devMaxTrauma/Drive/3DModel/ultrasonic-sensors-hc-sr04-1.snapshot.2/133-3.jpg

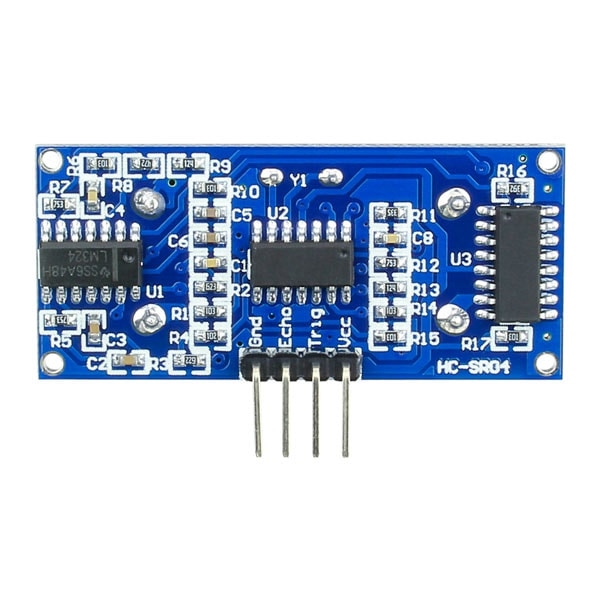
3DModel/ultrasonic-sensors-hc-sr04-1.snapshot.2/133-3.jpg
