devMaxTrauma/Drive/3DModel/ultrasonic-sensors-hc-sr04-1.snapshot.2/back.png

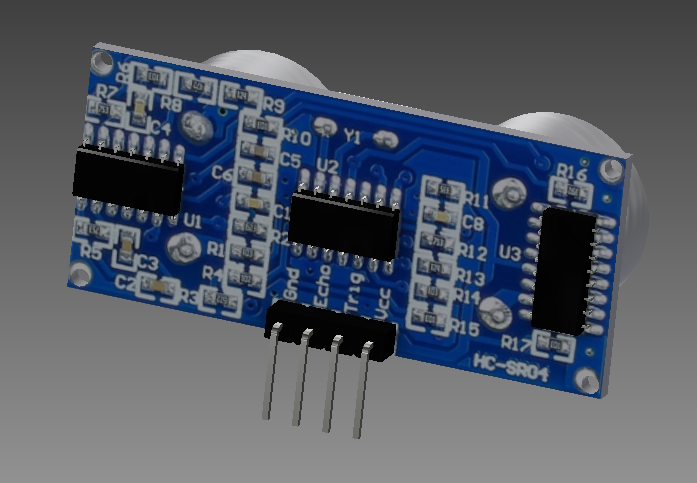
3DModel/ultrasonic-sensors-hc-sr04-1.snapshot.2/back.png
