devMaxTrauma/Drive/3DModel/ultrasonic-sensors-hc-sr04-1.snapshot.2/front.png

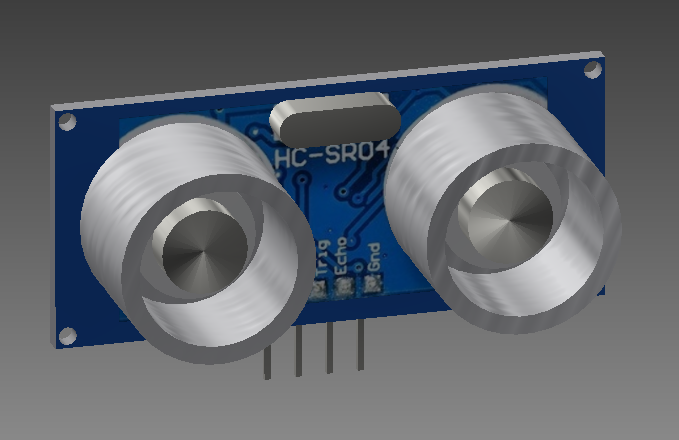
3DModel/ultrasonic-sensors-hc-sr04-1.snapshot.2/front.png
