devMaxTrauma/Drive/3DModel/ultrasonic-sensors-hc-sr04-1.snapshot.2/hc-sr04_.jpg

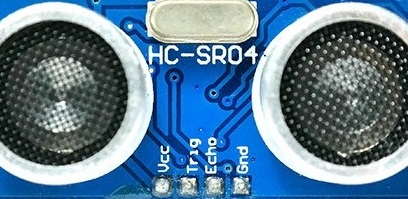
3DModel/ultrasonic-sensors-hc-sr04-1.snapshot.2/hc-sr04_.jpg
