devMaxTrauma/Drive/3DModel/usb-c-female-jrc-b008-1.snapshot.5/USB-C board JRC-B008.png

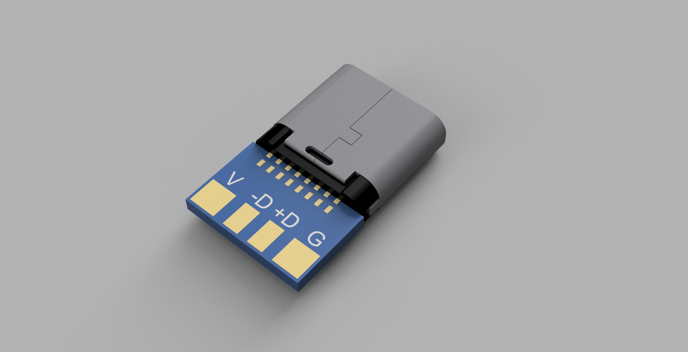
3DModel/usb-c-female-jrc-b008-1.snapshot.5/USB-C board JRC-B008.png
