devMaxTrauma/Drive/BlackBoard/vision layout.png

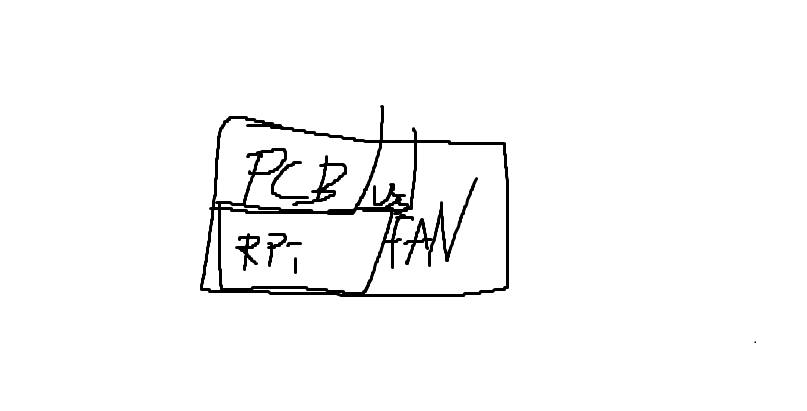
BlackBoard/vision layout.png
