devMaxTrauma/Drive/BlackBoard/상상도.png

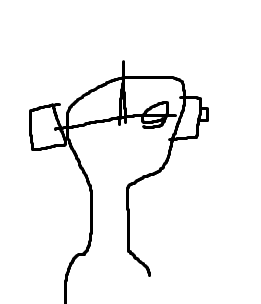
BlackBoard/상상도.png
