devMaxTrauma/Drive/Documents/rOS code new/ROS 24_09_30 code_page-0060.jpg

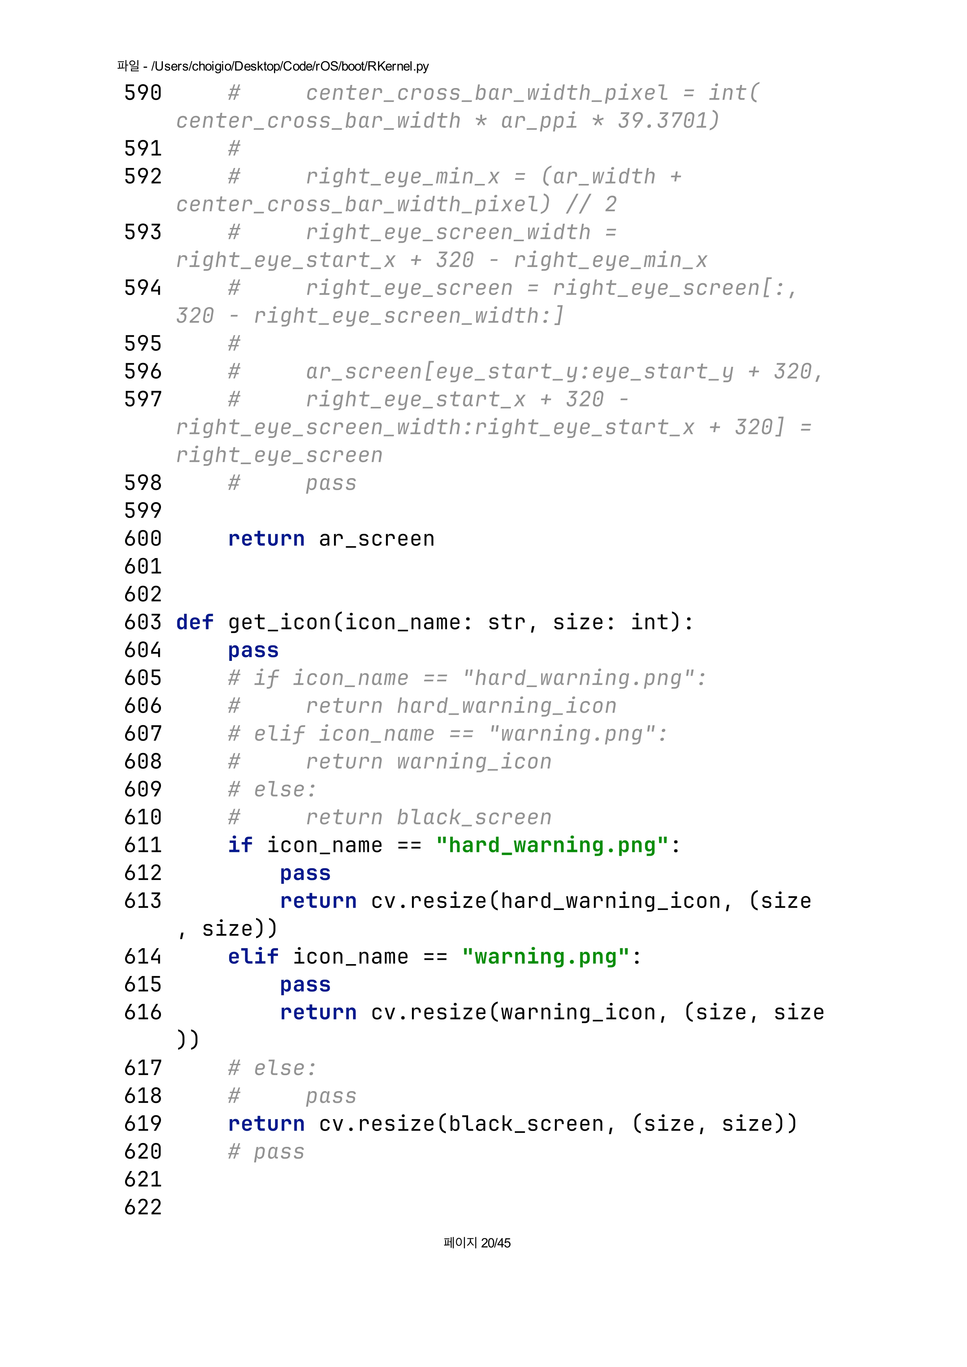
Documents/rOS code new/ROS 24_09_30 code_page-0060.jpg
