devMaxTrauma/Drive/Documents/ros code/ROS code 24_09_13_page-0054.jpg

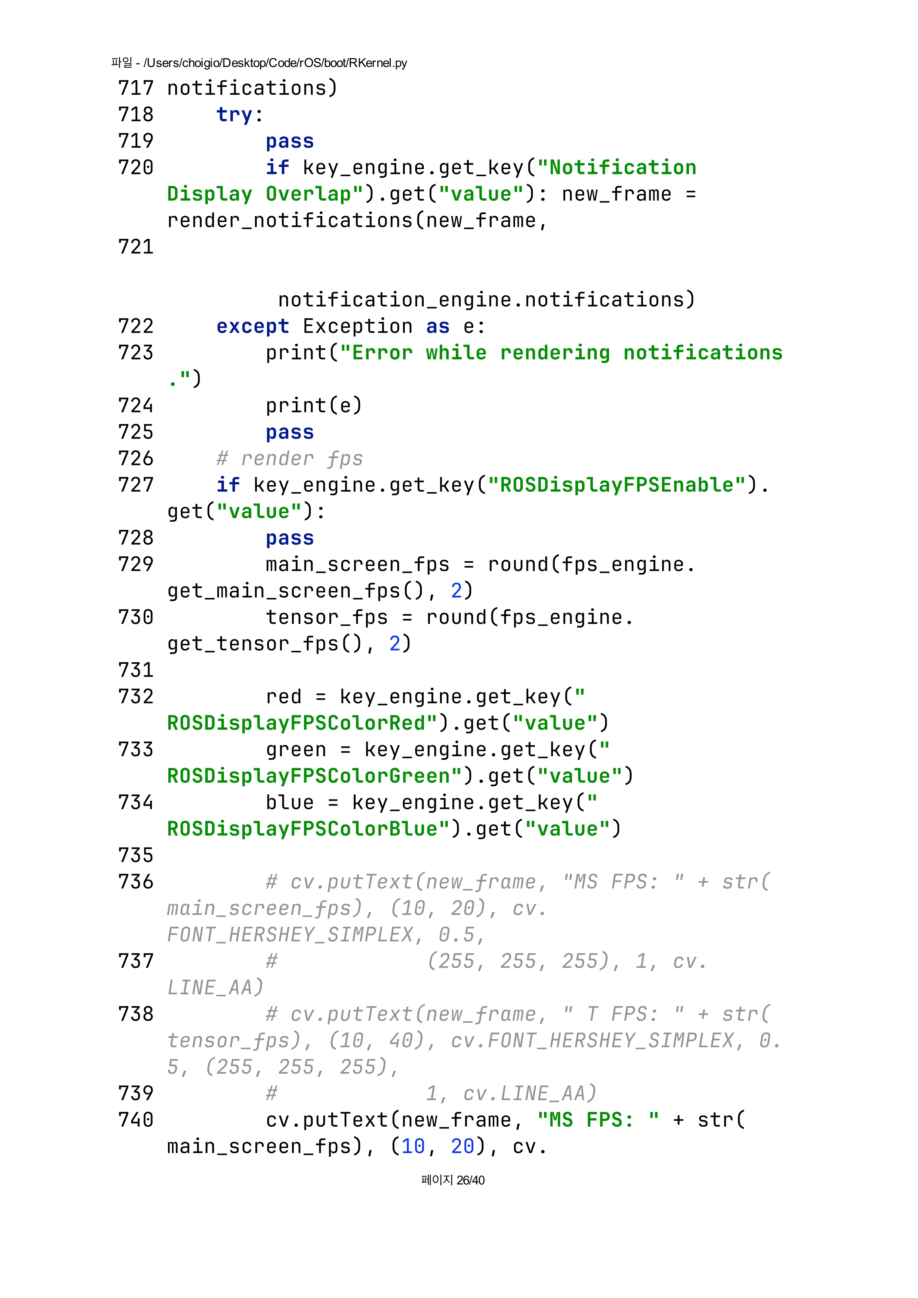
Documents/ros code/ROS code 24_09_13_page-0054.jpg
