devMaxTrauma/Drive/Pictures/devMaxTrauma.-2.jpg

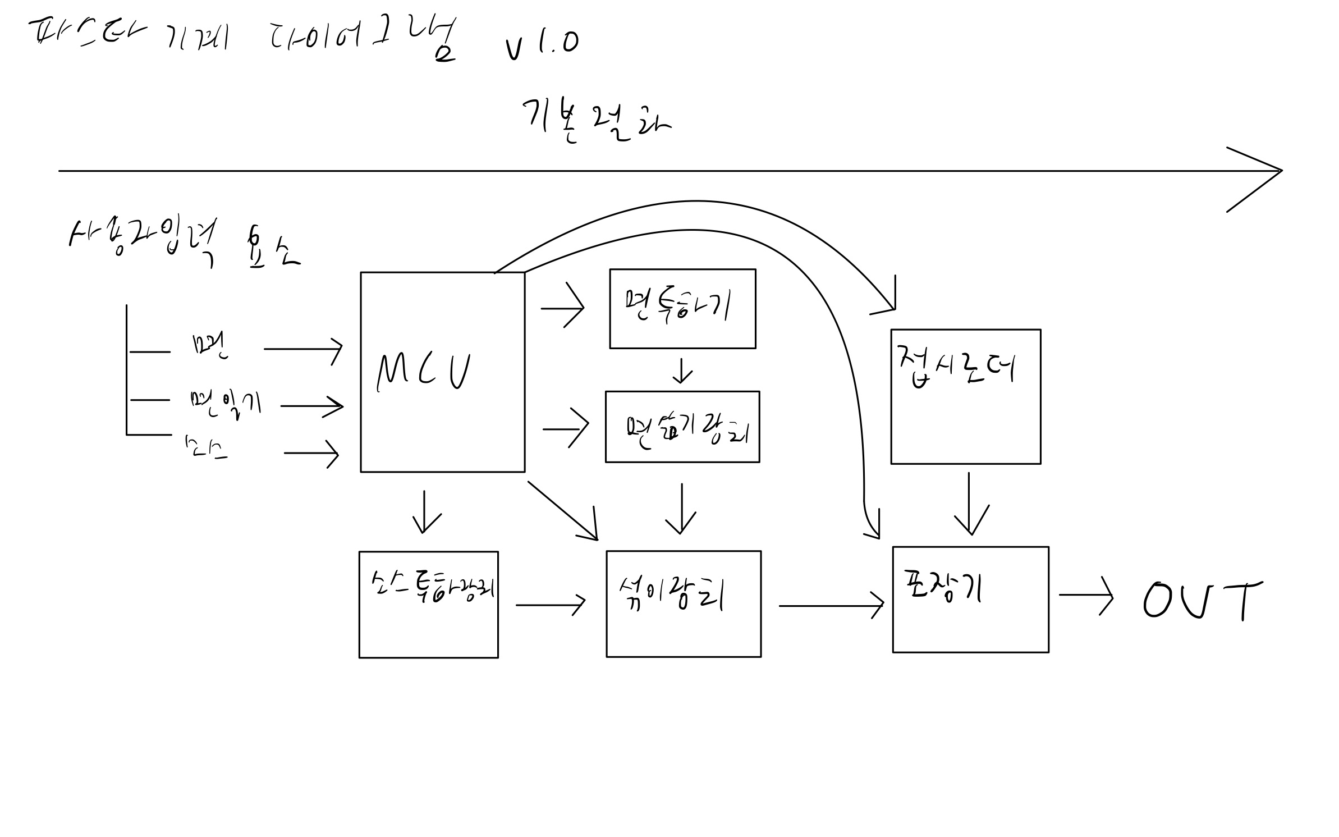
Pictures/devMaxTrauma.-2.jpg
