devMaxTrauma/Drive/BlackBoard/intec_name.dxf

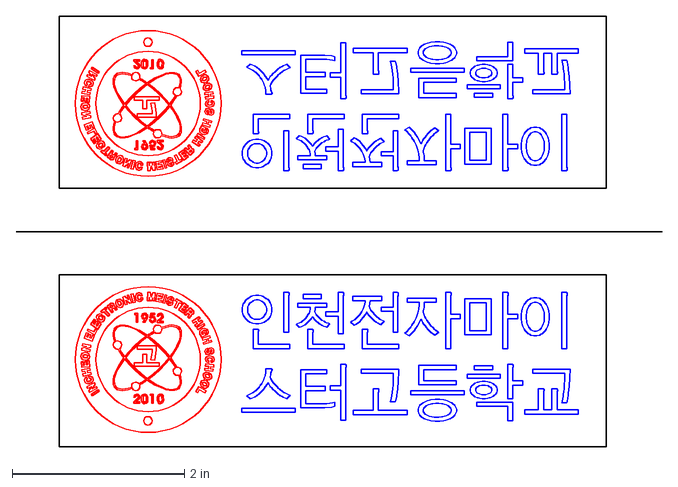
[picture p205: CAD file, 2024-12-01]
BlackBoard/intec_name.dxf
7.50 x 5.00 in
