devMaxTrauma/Drive/STL/2024_JUN_19 Order/LightSealGioV2.stl

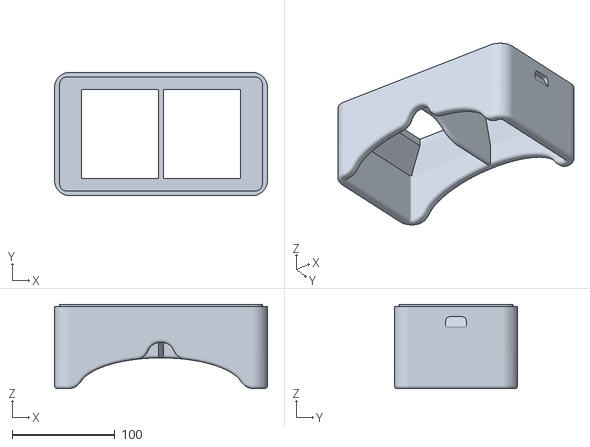
[picture p206: CAD file, 2024-12-01]
STL/2024_JUN_19 Order/LightSealGioV2.stl
207.0 x 120.0 x 82.1
