devMaxTrauma/Drive/STL/2024_MAY_28 Order/VisionFrameV2.stl

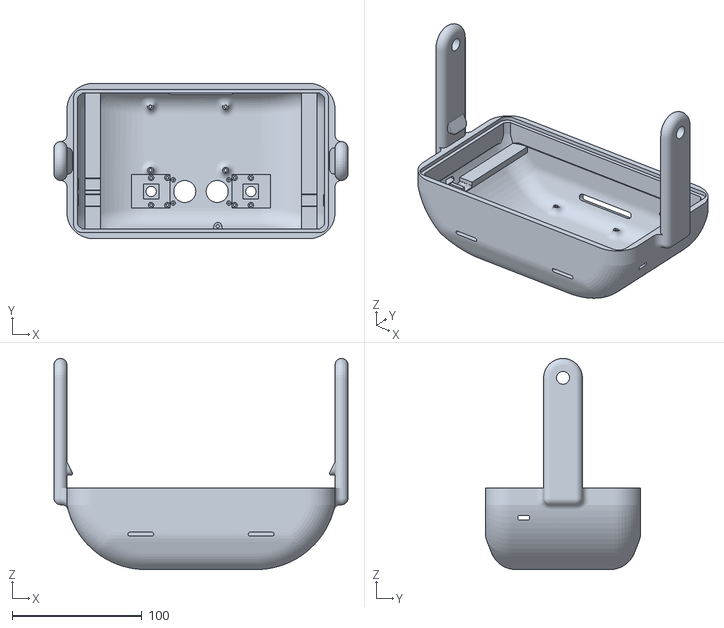
[picture p207: CAD file, 2024-12-01]
STL/2024_MAY_28 Order/VisionFrameV2.stl
227.0 x 120.0 x 163.0
