devMaxTrauma/Drive/ypanel.dxf

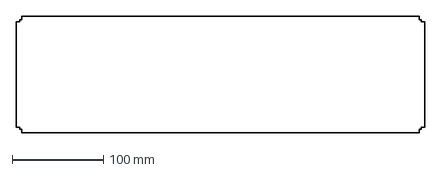
[picture p208: CAD file, 2024-12-01]
ypanel.dxf
448.0 x 128.0 mm
