devMaxTrauma/Drive/3DModel/raspberry-pi-5-2.snapshot.7/PARTS/DISPLAY_CONNECTOR/3.3 plastic.SLDPRT

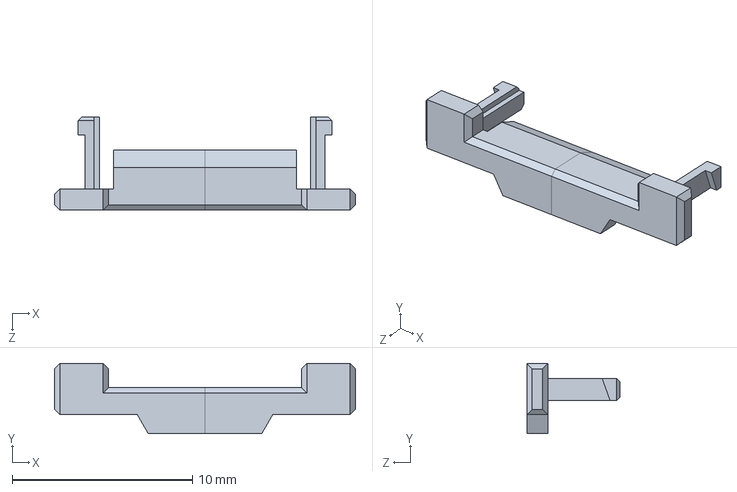
[picture p209: CAD file, 2024-12-01]
3DModel/raspberry-pi-5-2.snapshot.7/PARTS/DISPLAY_CONNECTOR/3.3 plastic.SLDPRT
16.7 x 3.90 x 5.18 mm
