devMaxTrauma/Drive/3DModel/raspberry-pi-5-2.snapshot.7/PARTS/GIGABIT_ETHERNET_PORT.SLDPRT

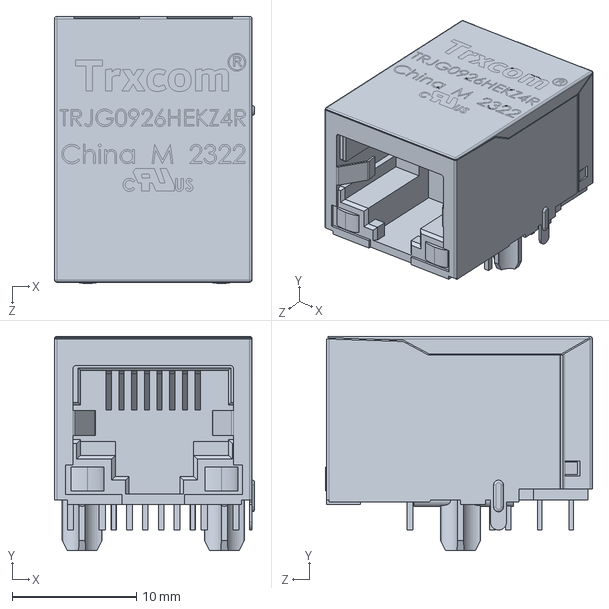
[picture p210: CAD file, 2024-12-01]
3DModel/raspberry-pi-5-2.snapshot.7/PARTS/GIGABIT_ETHERNET_PORT.SLDPRT
16.1 x 17.2 x 21.4 mm
