devMaxTrauma/Drive/3DModel/raspberry-pi-5-2.snapshot.7/PARTS/SD CARD/PART3_V1.SLDPRT

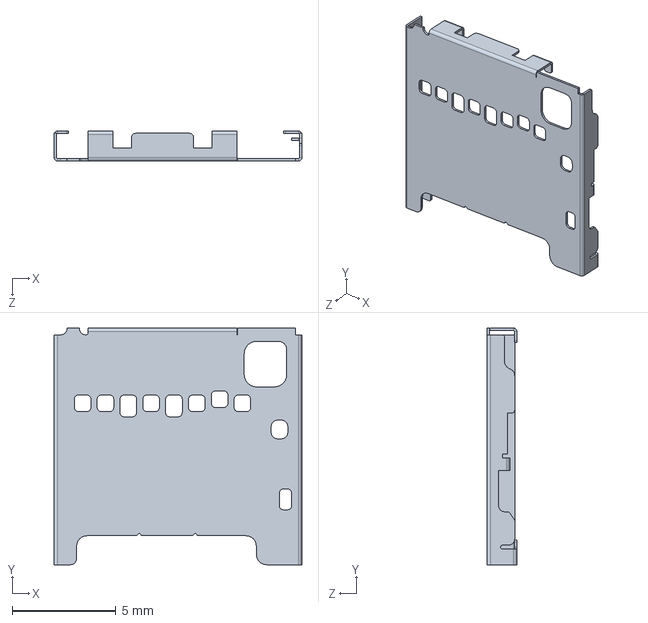
[picture p211: CAD file, 2024-12-01]
3DModel/raspberry-pi-5-2.snapshot.7/PARTS/SD CARD/PART3_V1.SLDPRT
11.9 x 11.4 x 1.45 mm
