devMaxTrauma/Drive/hanabi face.dxf

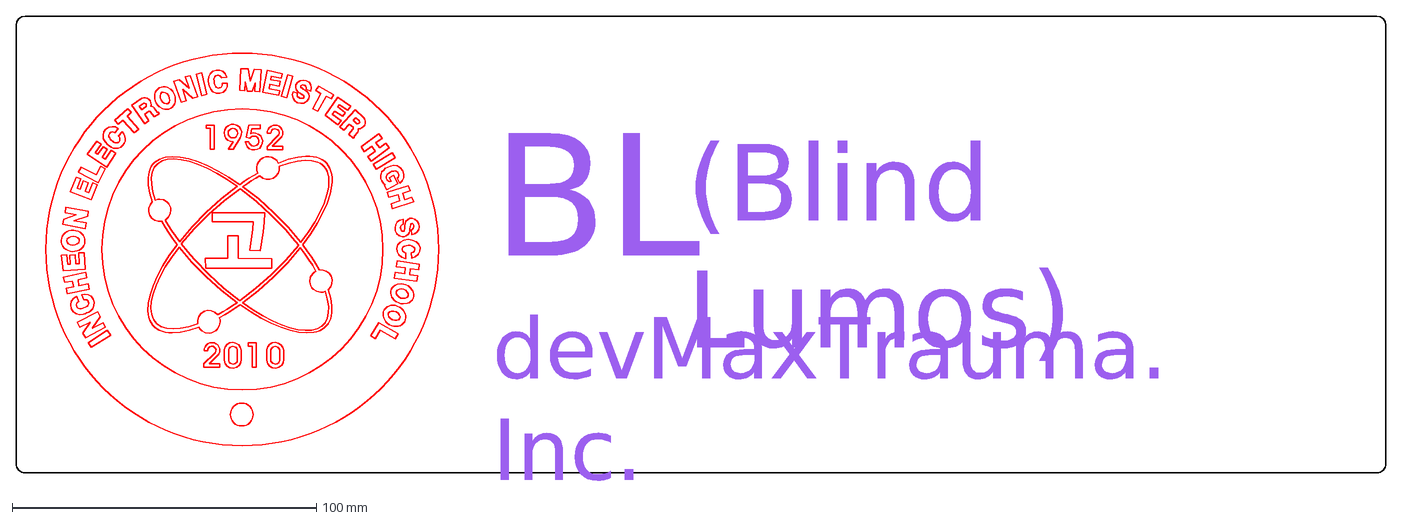
[picture p212: CAD file, 2024-12-01]
hanabi face.dxf
BL
(Blind Lumos)
devMaxTrauma. Inc.
