devMaxTrauma/Drive/STL/visionFrame.stl

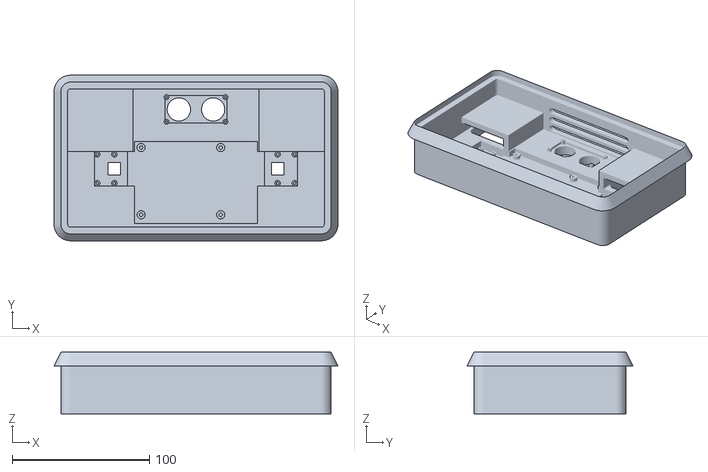
[picture p213: CAD file, 2024-12-01]
STL/visionFrame.stl
207.0 x 120.8 x 45.0
