devMaxTrauma/Drive/3DModel/raspberry-pi-5-2.snapshot.7/PARTS/DISPLAY_CONNECTOR/1.1 part 1 metal pin.SLDPRT

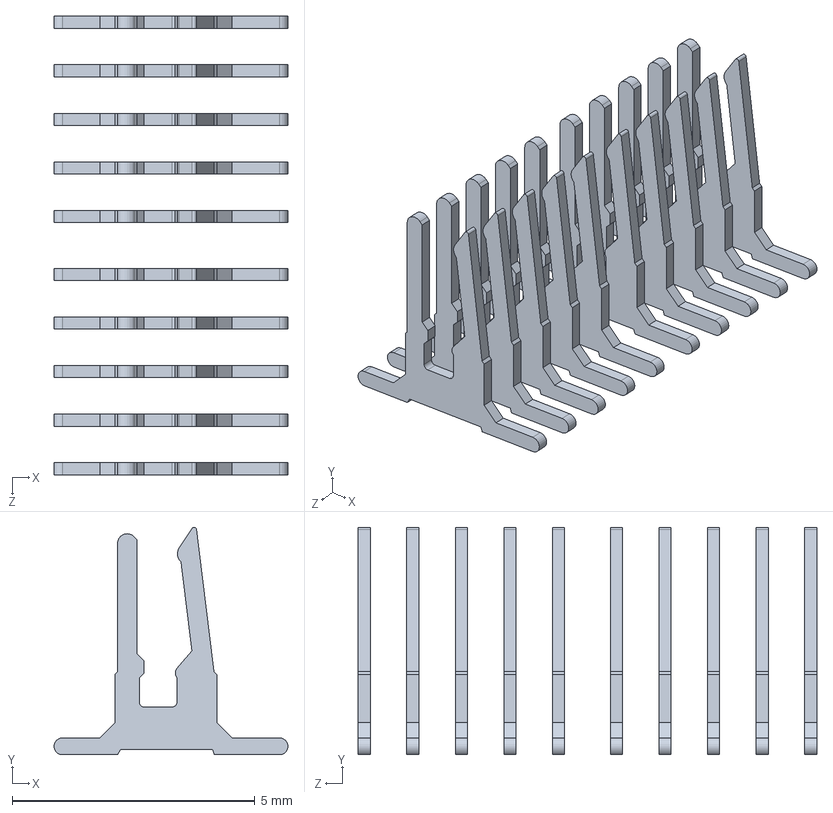
[picture p214: CAD file, 2024-12-01]
3DModel/raspberry-pi-5-2.snapshot.7/PARTS/DISPLAY_CONNECTOR/1.1 part 1 metal pin.SLDPRT
4.82 x 4.69 x 9.45 mm
