devMaxTrauma/Drive/BlackBoard/rubberjoindxf.dxf

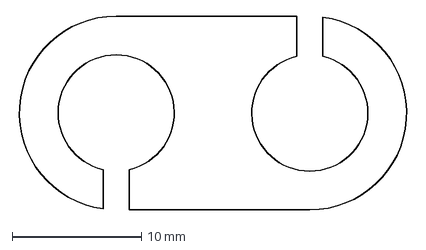
[picture p216: CAD file, 2024-12-01]
BlackBoard/rubberjoindxf.dxf
30.5 x 15.0 mm
