devMaxTrauma/Drive/STL/2024_AUG_19 Order 2/FANCATCHER.stl

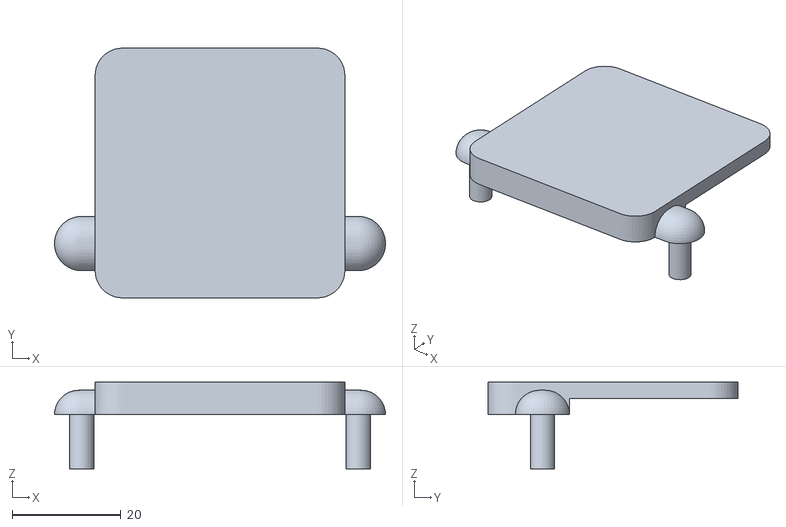
[picture p217: CAD file, 2024-12-01]
STL/2024_AUG_19 Order 2/FANCATCHER.stl
61.0 x 46.0 x 16.0
