devMaxTrauma/Drive/STL/VisionFrameV2.1 testArticle.stl

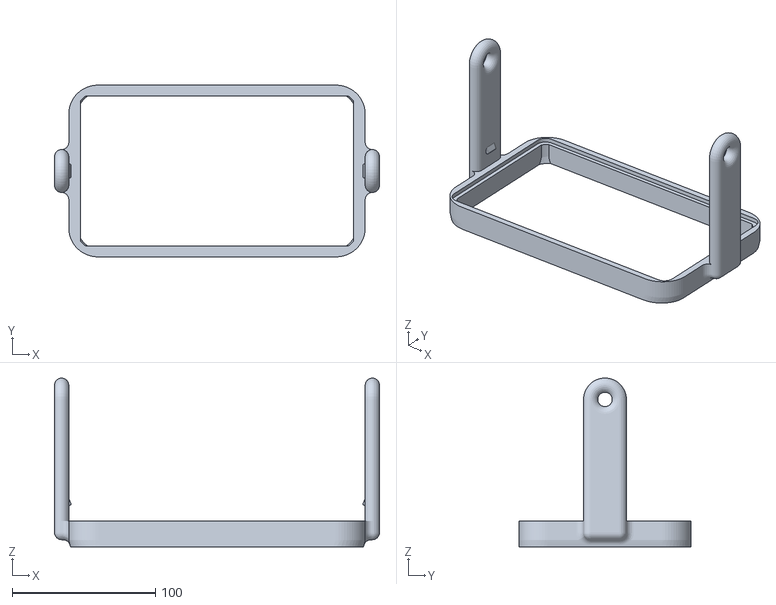
[picture p218: CAD file, 2024-12-01]
STL/VisionFrameV2.1 testArticle.stl
227.0 x 120.0 x 118.0
