devMaxTrauma/Drive/xpanel.dxf

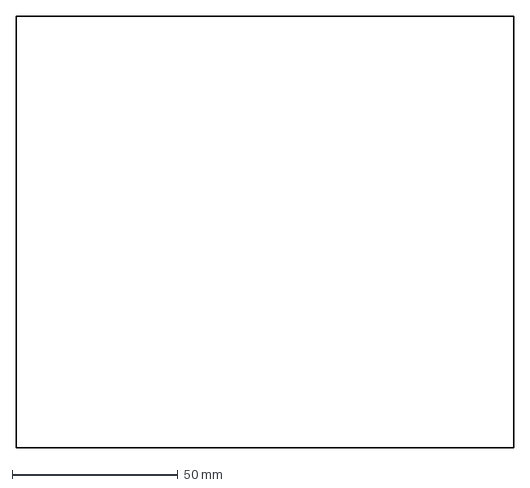
[picture p219: CAD file, 2024-12-01]
xpanel.dxf
150.0 x 130.0 mm
