devMaxTrauma/Drive/3DModel/raspberry-pi-5-2.snapshot.7/PARTS/3.0_PIN_HEADER_10.SLDPRT

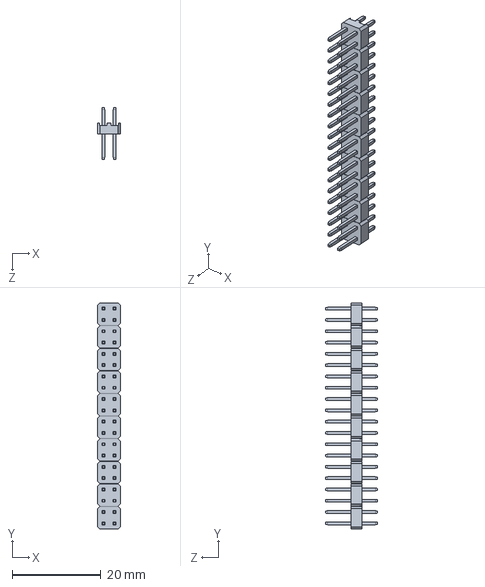
[picture p220: CAD file, 2024-12-01]
3DModel/raspberry-pi-5-2.snapshot.7/PARTS/3.0_PIN_HEADER_10.SLDPRT
5.08 x 50.8 x 11.8 mm
