devMaxTrauma/Drive/hanabi face2.dxf

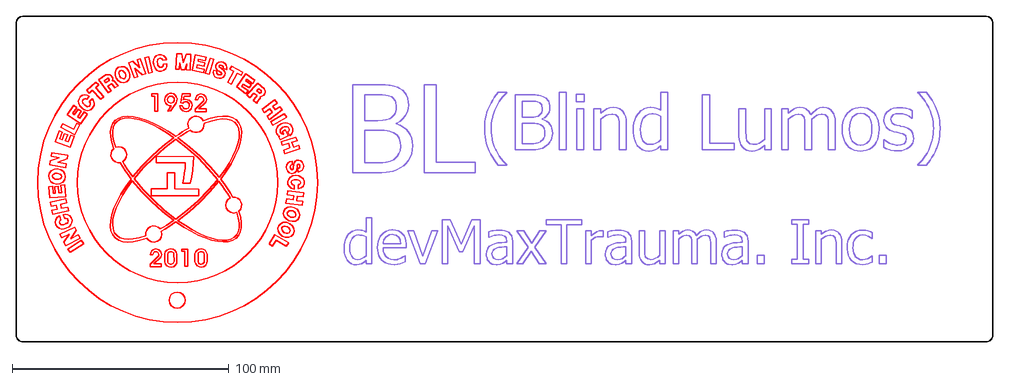
[picture p221: CAD file, 2024-12-01]
hanabi face2.dxf
450.0 x 150.0 mm
