devMaxTrauma/Drive/STL/2024_AUG_19 Order 2/BatPackCaseCoverV2.stl

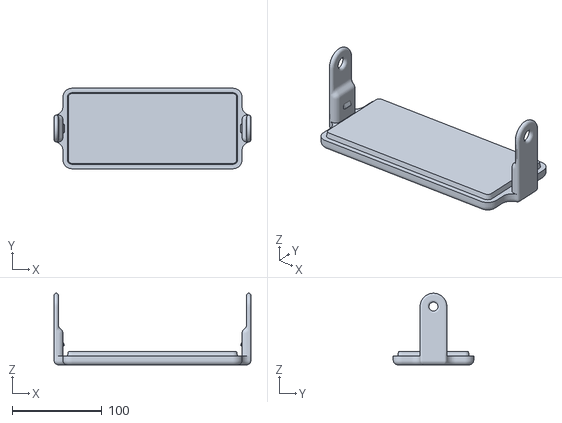
[picture p222: CAD file, 2024-12-01]
STL/2024_AUG_19 Order 2/BatPackCaseCoverV2.stl
220.0 x 90.0 x 80.0
