devMaxTrauma/Drive/STL/2024_JUN_19 Order/VisionFrameV2.stl

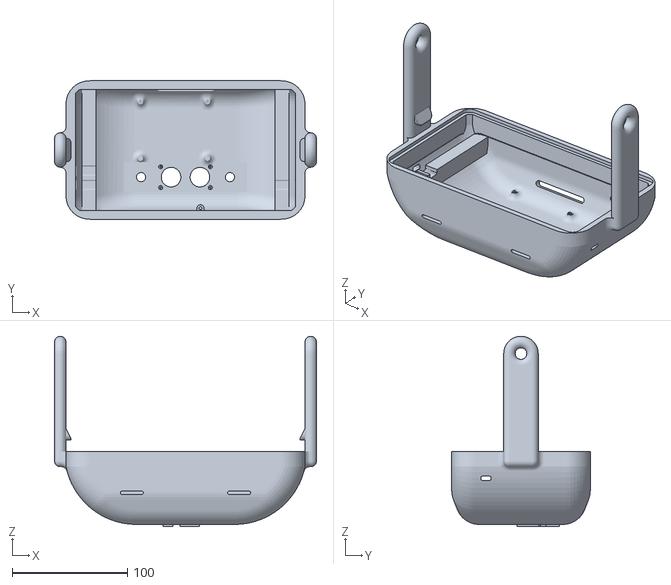
[picture p223: CAD file, 2024-12-01]
STL/2024_JUN_19 Order/VisionFrameV2.stl
227.0 x 120.0 x 165.0
