devMaxTrauma/Drive/3DModel/raspberry-pi-5-2.snapshot.7/PARTS/FEMALE_MICRO_HDMI_CONNECTOR.SLDPRT

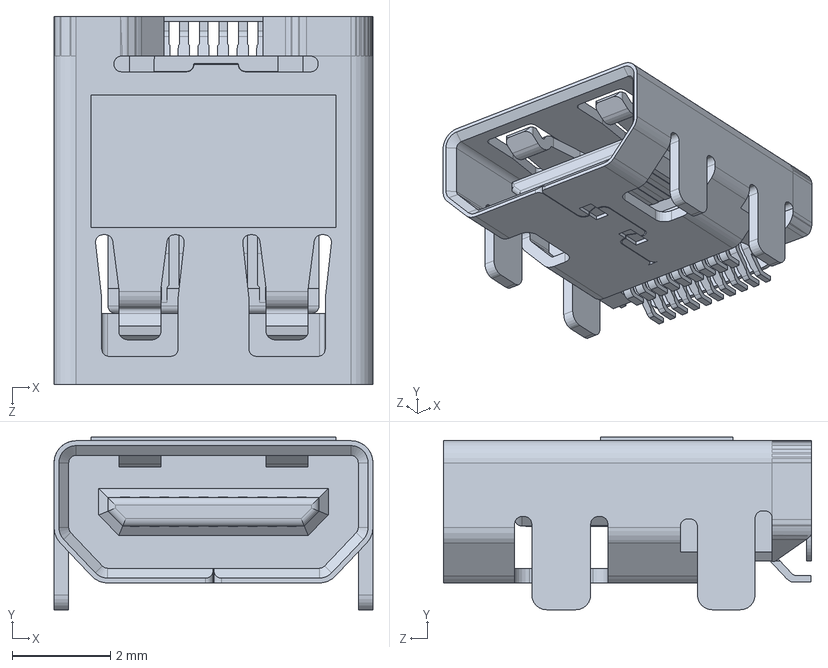
[picture p224: CAD file, 2024-12-01]
3DModel/raspberry-pi-5-2.snapshot.7/PARTS/FEMALE_MICRO_HDMI_CONNECTOR.SLDPRT
6.50 x 3.52 x 7.50 mm
