devMaxTrauma/Drive/3DModel/raspberry-pi-5-2.snapshot.7/PARTS/CAMERA_DISPLAY_2.SLDPRT

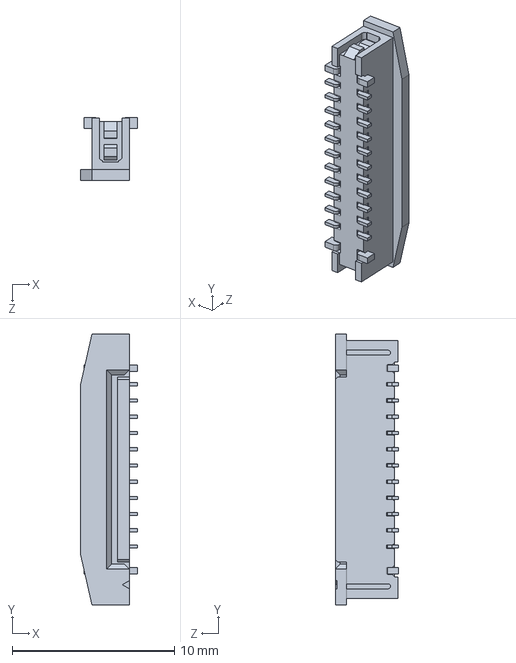
[picture p225: CAD file, 2024-12-01]
3DModel/raspberry-pi-5-2.snapshot.7/PARTS/CAMERA_DISPLAY_2.SLDPRT
3.50 x 16.7 x 3.90 mm
