devMaxTrauma/Drive/STL/2024_JUN_19 Order/BatPackCaseCover.stl

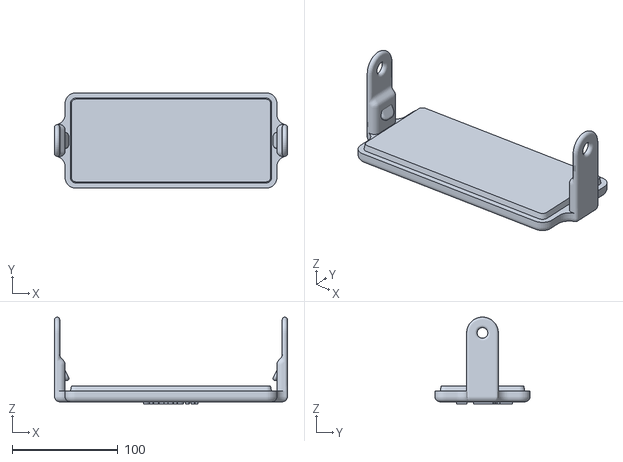
[picture p226: CAD file, 2024-12-01]
STL/2024_JUN_19 Order/BatPackCaseCover.stl
220.0 x 90.0 x 82.0
