devMaxTrauma/Drive/3DModel/raspberry-pi-5-2.snapshot.7/PARTS/METAL_PLATE..SLDPRT

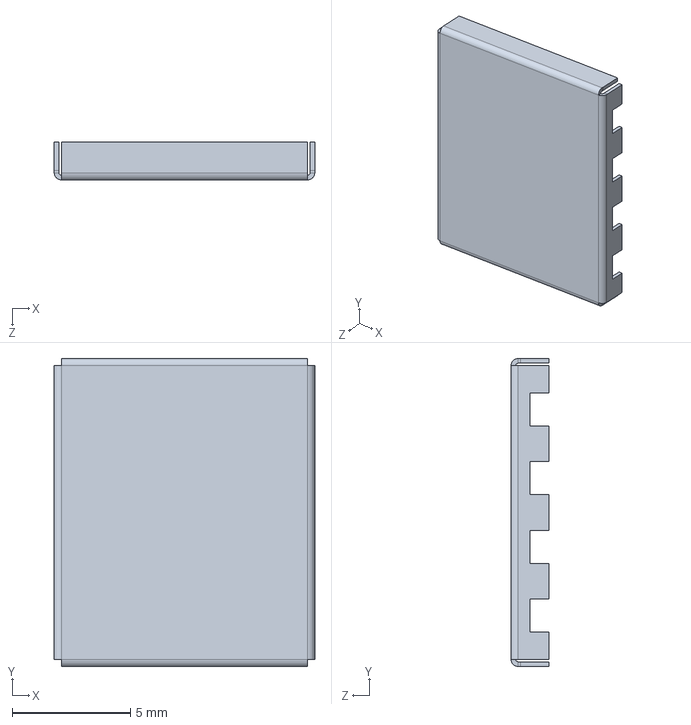
[picture p227: CAD file, 2024-12-01]
3DModel/raspberry-pi-5-2.snapshot.7/PARTS/METAL_PLATE..SLDPRT
11.0 x 13.0 x 1.60 mm
