devMaxTrauma/Drive/3DModel/raspberry-pi-5-2.snapshot.7/PARTS/RP1_CO_CONTROLLER.SLDPRT

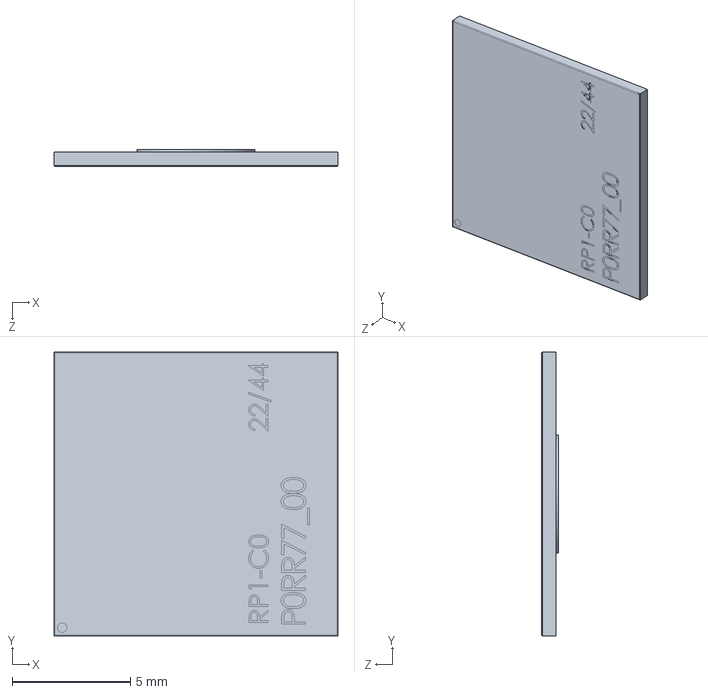
[picture p228: CAD file, 2024-12-01]
3DModel/raspberry-pi-5-2.snapshot.7/PARTS/RP1_CO_CONTROLLER.SLDPRT
12.0 x 12.0 x 0.7 mm
