devMaxTrauma/Drive/3DModel/raspberry-pi-5-2.snapshot.7/PARTS/BUTTON_MINI.SLDPRT

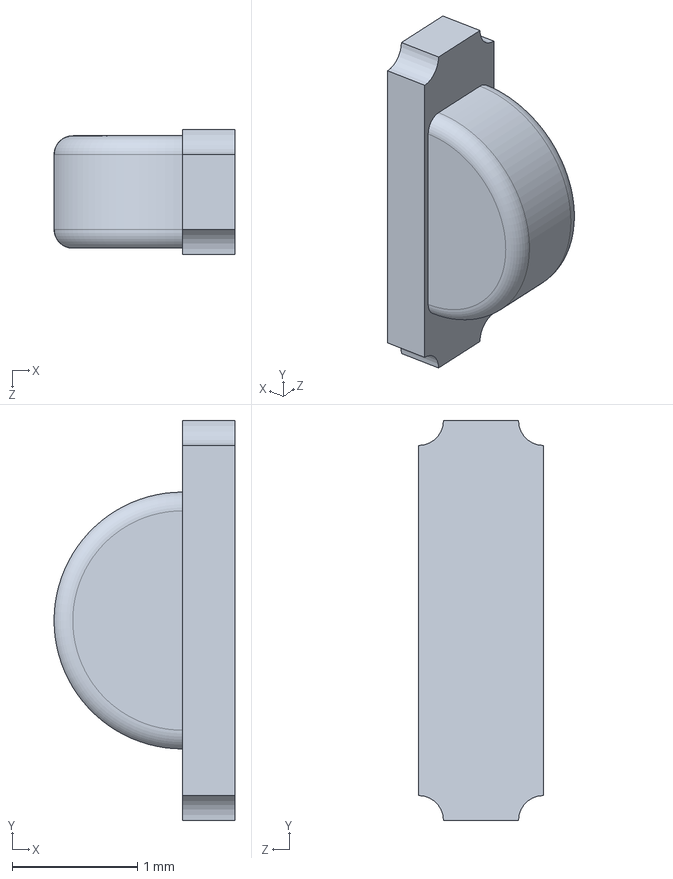
[picture p229: CAD file, 2024-12-01]
3DModel/raspberry-pi-5-2.snapshot.7/PARTS/BUTTON_MINI.SLDPRT
1.45 x 3.20 x 1 mm
