devMaxTrauma/Drive/3DModel/raspberry-pi-5-2.snapshot.7/PARTS/2.0_PIN_HEADER.SLDPRT

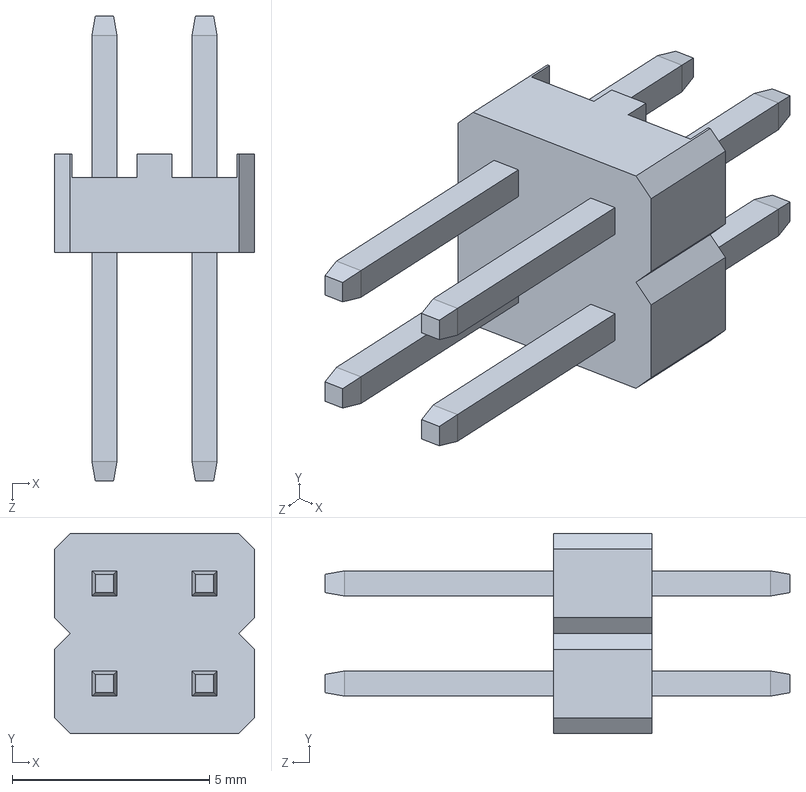
[picture p230: CAD file, 2024-12-01]
3DModel/raspberry-pi-5-2.snapshot.7/PARTS/2.0_PIN_HEADER.SLDPRT
5.08 x 5.08 x 11.8 mm
