devMaxTrauma/Drive/3DModel/raspberry-pi-5-2.snapshot.7/PARTS/9FD77_D9WHV.SLDPRT

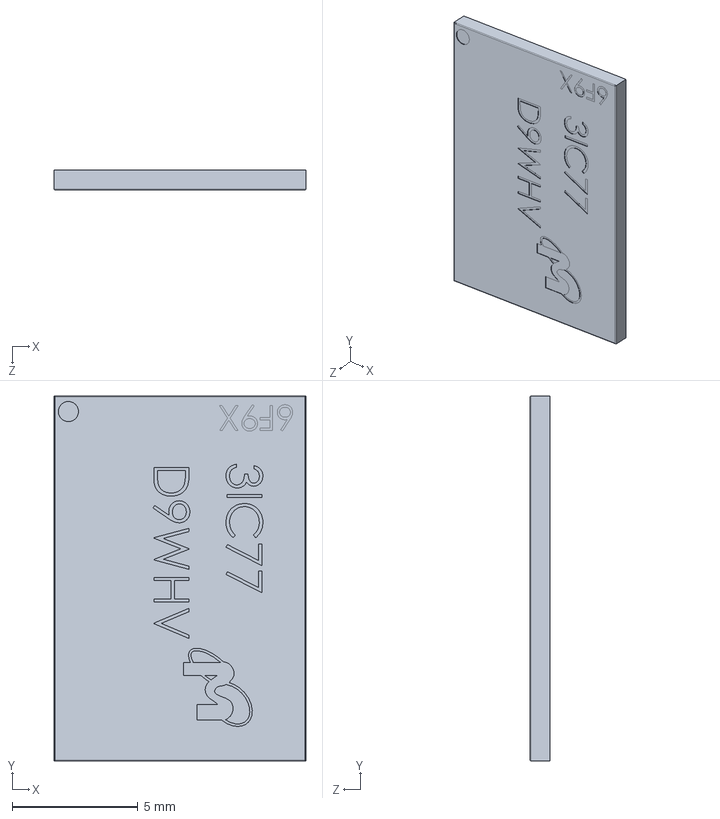
[picture p231: CAD file, 2024-12-01]
3DModel/raspberry-pi-5-2.snapshot.7/PARTS/9FD77_D9WHV.SLDPRT
10.0 x 14.5 x 0.8 mm
