devMaxTrauma/Drive/3DModel/raspberry-pi-5-2.snapshot.7/PARTS/MxL.SLDPRT

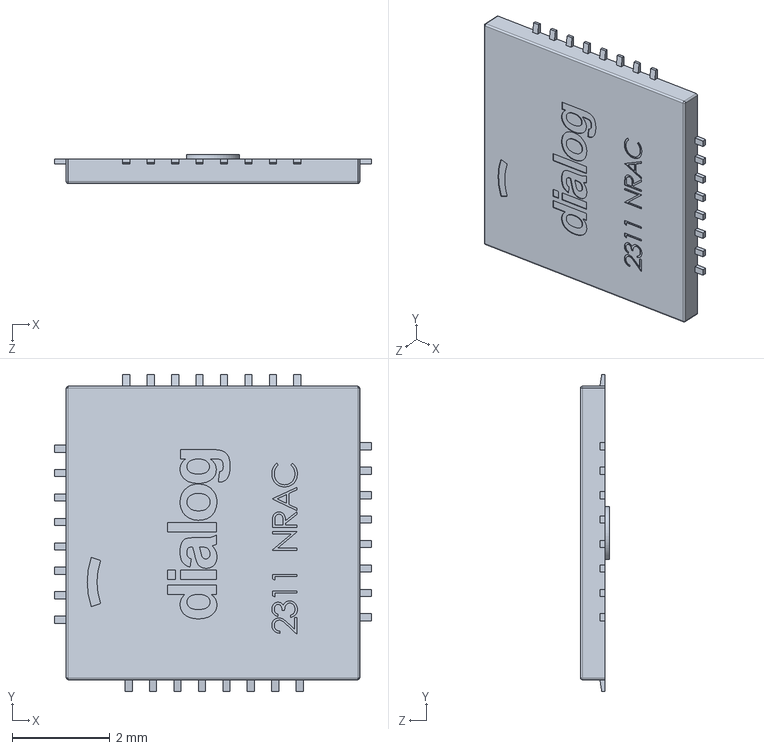
[picture p233: CAD file, 2024-12-01]
3DModel/raspberry-pi-5-2.snapshot.7/PARTS/MxL.SLDPRT
6.48 x 6.48 x 0.6 mm
