devMaxTrauma/Drive/3DModel/raspberry-pi-5-2.snapshot.7/PARTS/PLATE_RASPBERRY_PI_5.SLDPRT

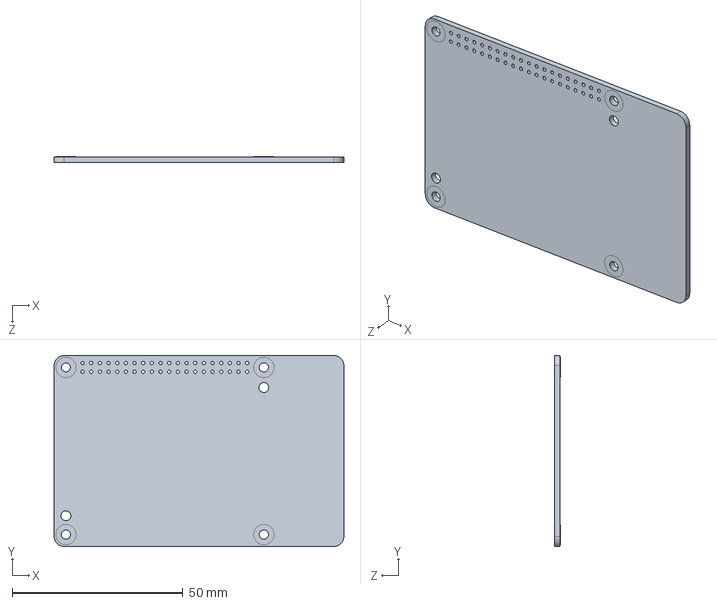
[picture p234: CAD file, 2024-12-01]
3DModel/raspberry-pi-5-2.snapshot.7/PARTS/PLATE_RASPBERRY_PI_5.SLDPRT
85.0 x 56.0 x 1.70 mm
