devMaxTrauma/Drive/3DModel/raspberry-pi-5-2.snapshot.7/PARTS/BUTTON_2.SLDPRT

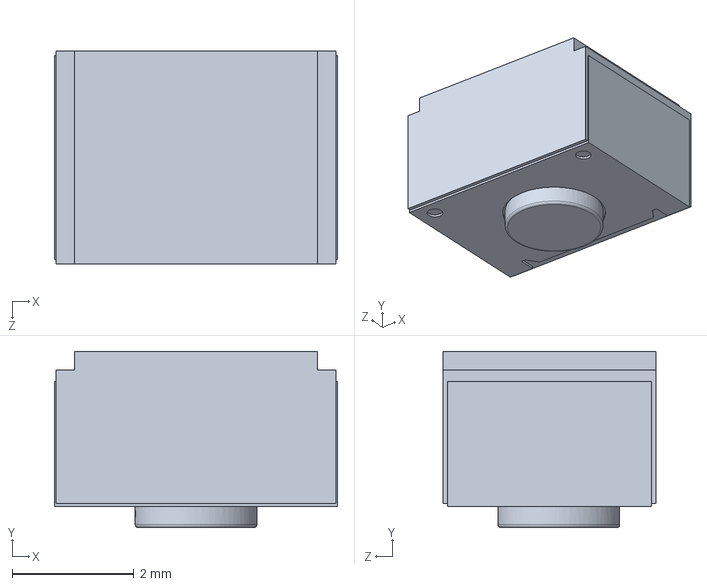
[picture p235: CAD file, 2024-12-01]
3DModel/raspberry-pi-5-2.snapshot.7/PARTS/BUTTON_2.SLDPRT
4.65 x 2.90 x 3.50 mm
