devMaxTrauma/Drive/3DModel/raspberry-pi-5-2.snapshot.7/PARTS/GIGABIT_ETHERNET_TRANSCEIVER.SLDPRT

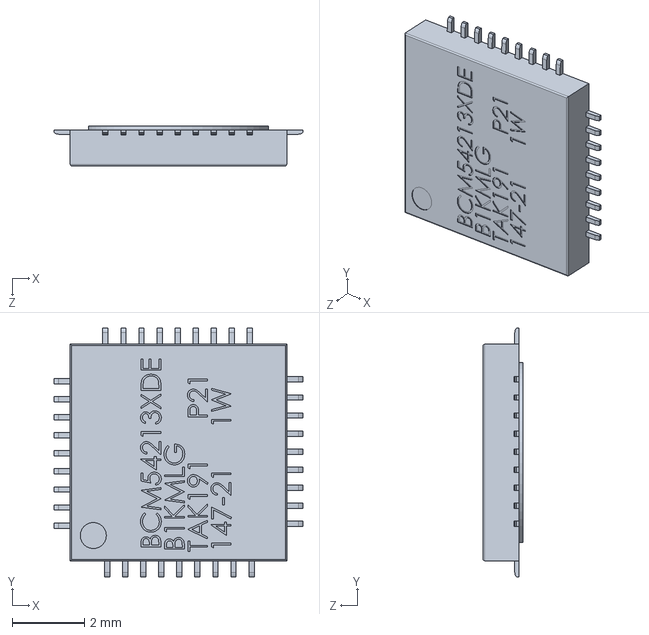
[picture p236: CAD file, 2024-12-01]
3DModel/raspberry-pi-5-2.snapshot.7/PARTS/GIGABIT_ETHERNET_TRANSCEIVER.SLDPRT
6.90 x 6.90 x 1.10 mm
