devMaxTrauma/Drive/3DModel/raspberry-pi-5-2.snapshot.7/PARTS/CONNECT_V1.SLDPRT

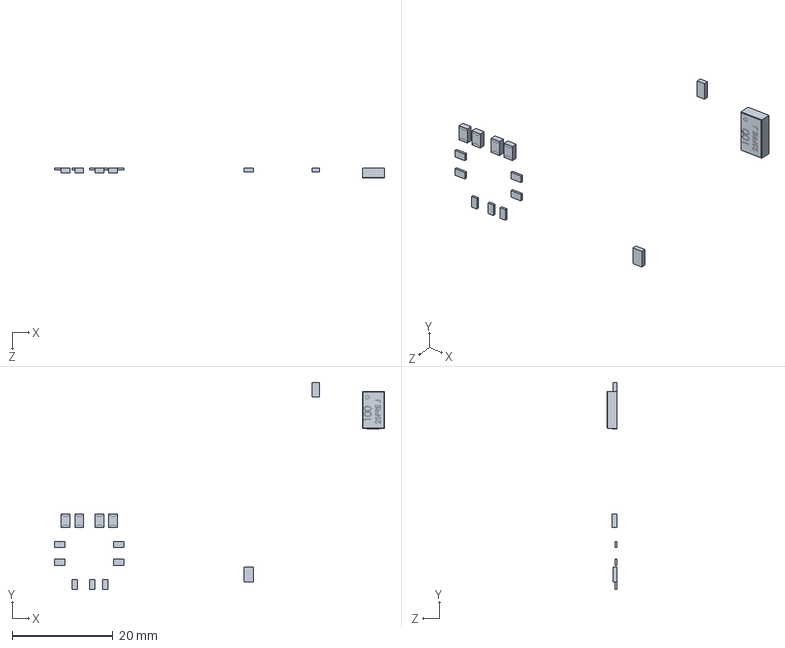
[picture p237: CAD file, 2024-12-01]
3DModel/raspberry-pi-5-2.snapshot.7/PARTS/CONNECT_V1.SLDPRT
65.4 x 41.1 x 2.00 mm
