devMaxTrauma/Drive/3DModel/raspberry-pi-5-2.snapshot.7/PARTS/STOCK_2.SLDPRT

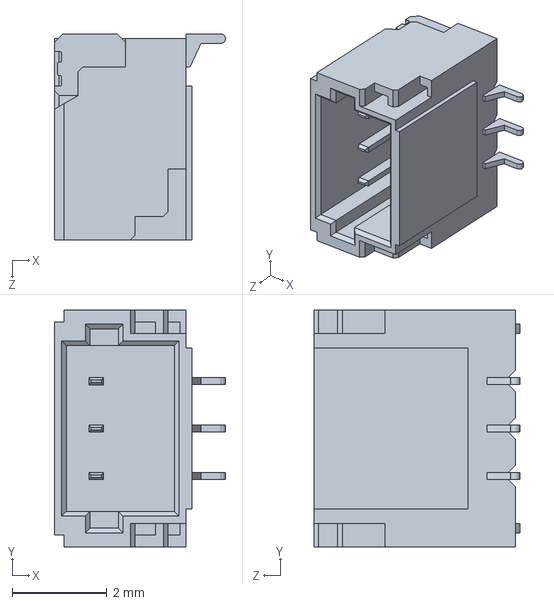
[picture p239: CAD file, 2024-12-01]
3DModel/raspberry-pi-5-2.snapshot.7/PARTS/STOCK_2.SLDPRT
3.61 x 5.00 x 4.35 mm
