devMaxTrauma/Drive/3DModel/raspberry-pi-5-2.snapshot.7/PARTS/BROADCOM_1.SLDPRT

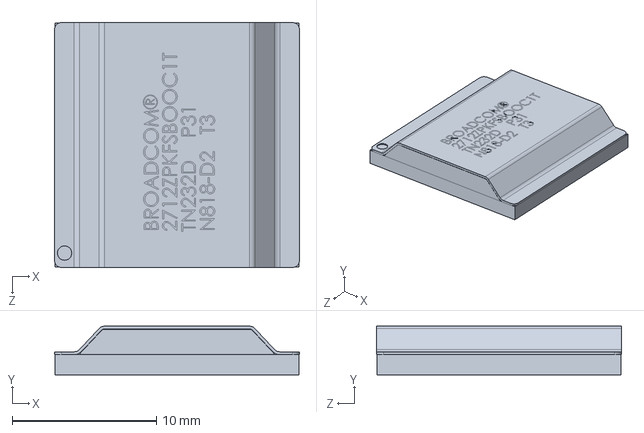
[picture p240: CAD file, 2024-12-01]
3DModel/raspberry-pi-5-2.snapshot.7/PARTS/BROADCOM_1.SLDPRT
17.0 x 3.38 x 17.0 mm
