devMaxTrauma/Drive/3DModel/raspberry-pi-5-2.snapshot.7/PARTS/2xUSB_2.0_PORT.SLDPRT

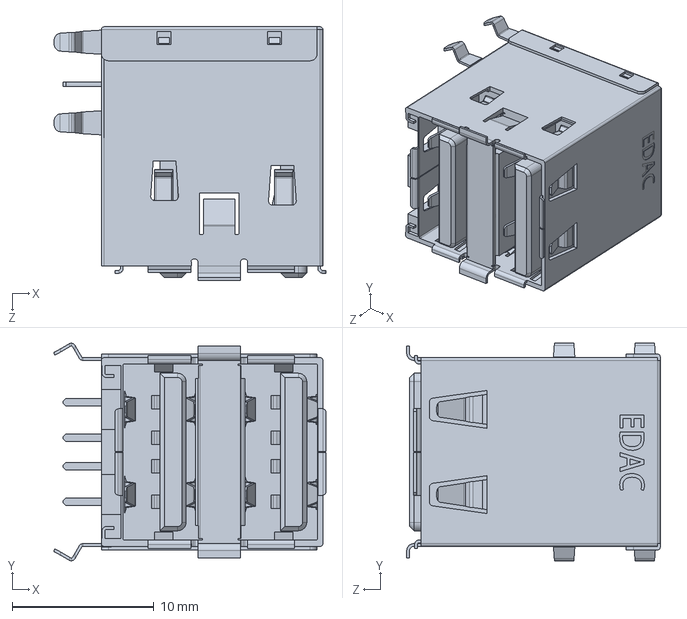
[picture p241: CAD file, 2024-12-01]
3DModel/raspberry-pi-5-2.snapshot.7/PARTS/2xUSB_2.0_PORT.SLDPRT
19.2 x 15.3 x 17.9 mm
